joelmathewsssss/HammerHacks-II-Badge-PCB/assets/bird.png

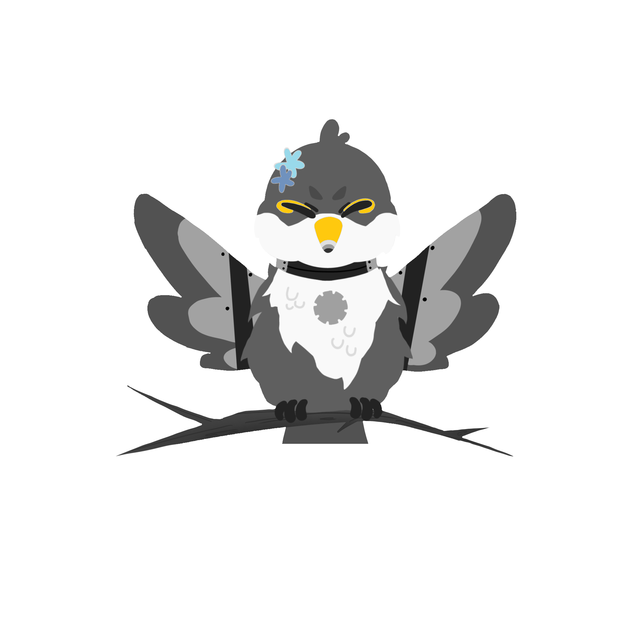
assets/bird.png
