joelmathewsssss/HammerHacks-II-Badge-PCB/assets/PICS/image.png

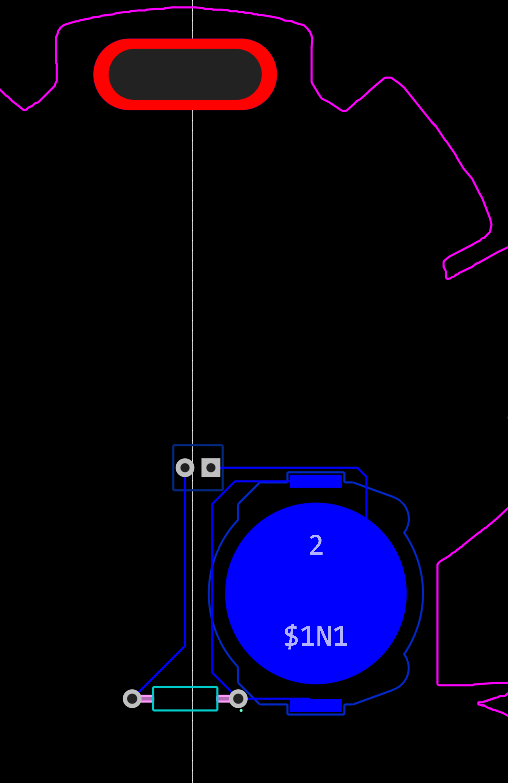
assets/PICS/image.png
