joelmathewsssss/HammerHacks-II-Badge-PCB/assets/PICS/PXL_20260712_225930694.jpg

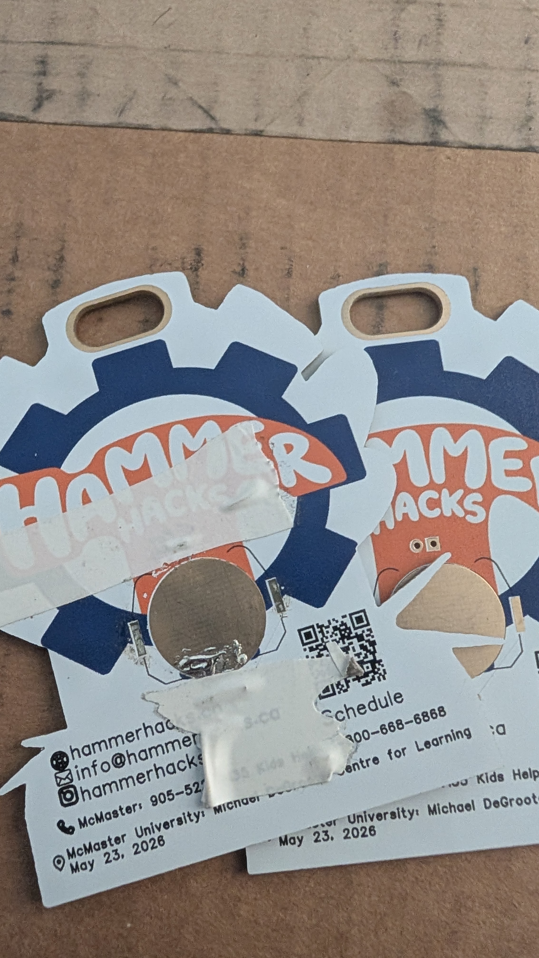
assets/PICS/PXL_20260712_225930694.jpg
