joelmathewsssss/HammerHacks-II-Badge-PCB/assets/PICS/PXL_20260712_232706811.jpg

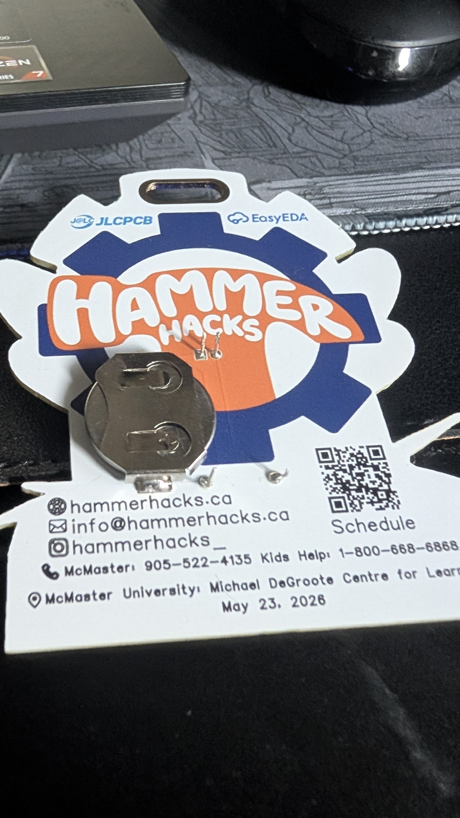
assets/PICS/PXL_20260712_232706811.jpg
