joelmathewsssss/HammerHacks-II-Badge-PCB/assets/PICS/Screenshot 2026-03-13 092637.png

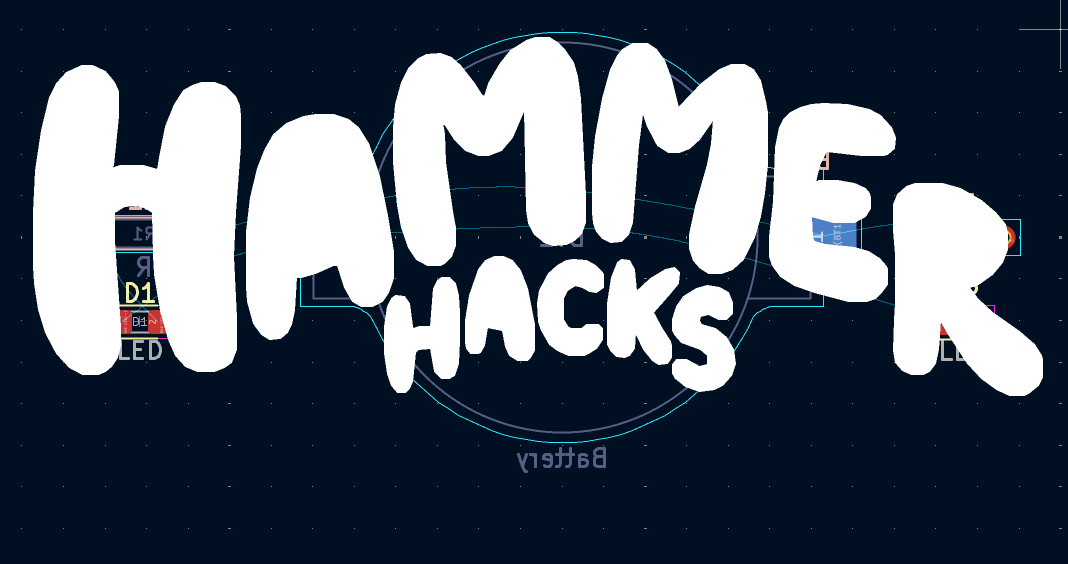
assets/PICS/Screenshot 2026-03-13 092637.png
