joelmathewsssss/HammerHacks-II-Badge-PCB/assets/PICS/Screenshot 2026-03-14 190404.png

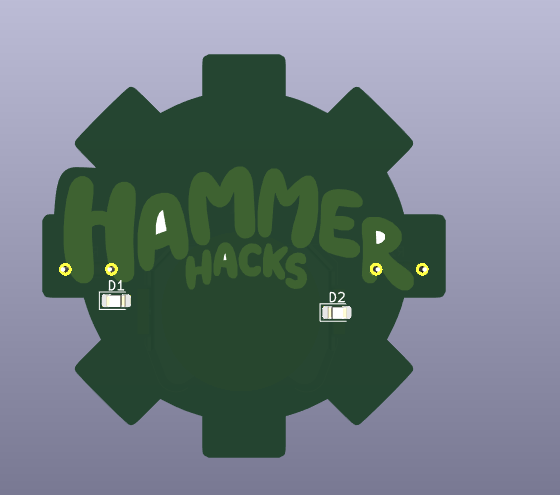
assets/PICS/Screenshot 2026-03-14 190404.png
