joelmathewsssss/HammerHacks-II-Badge-PCB/assets/PICS/Screenshot 2026-03-18 231449.png

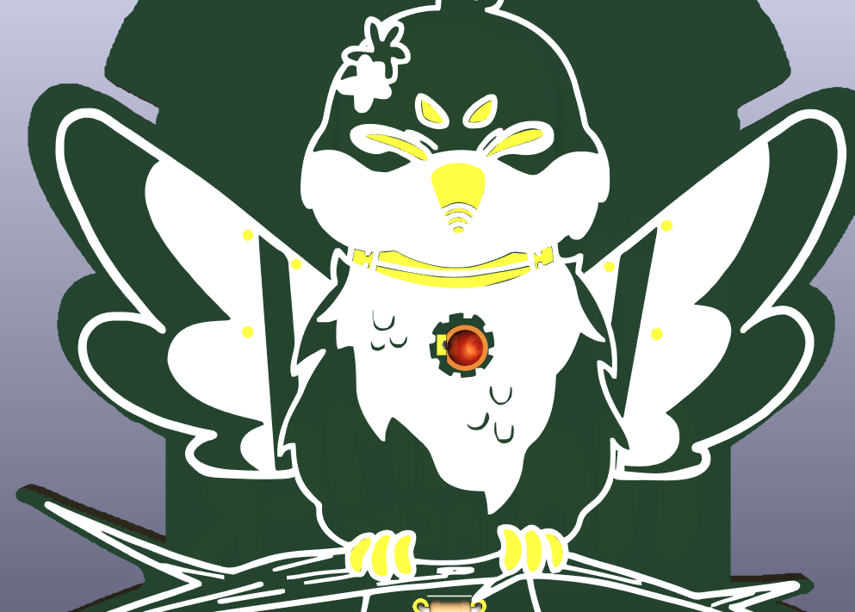
assets/PICS/Screenshot 2026-03-18 231449.png
