joelmathewsssss/HammerHacks-II-Badge-PCB/assets/PICS/Screenshot 2026-03-18 235800.png

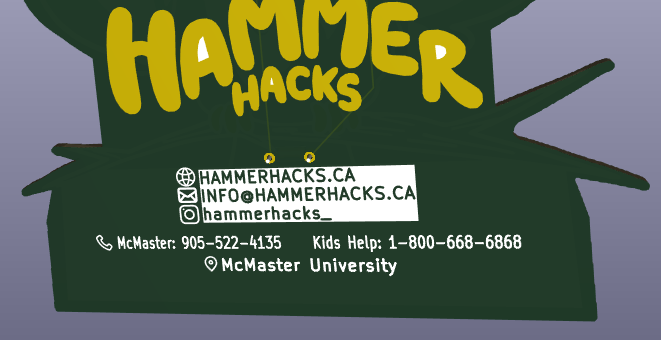
assets/PICS/Screenshot 2026-03-18 235800.png
