joelmathewsssss/HammerHacks-II-Badge-PCB/assets/PICS/Screenshot 2026-03-19 003215.png

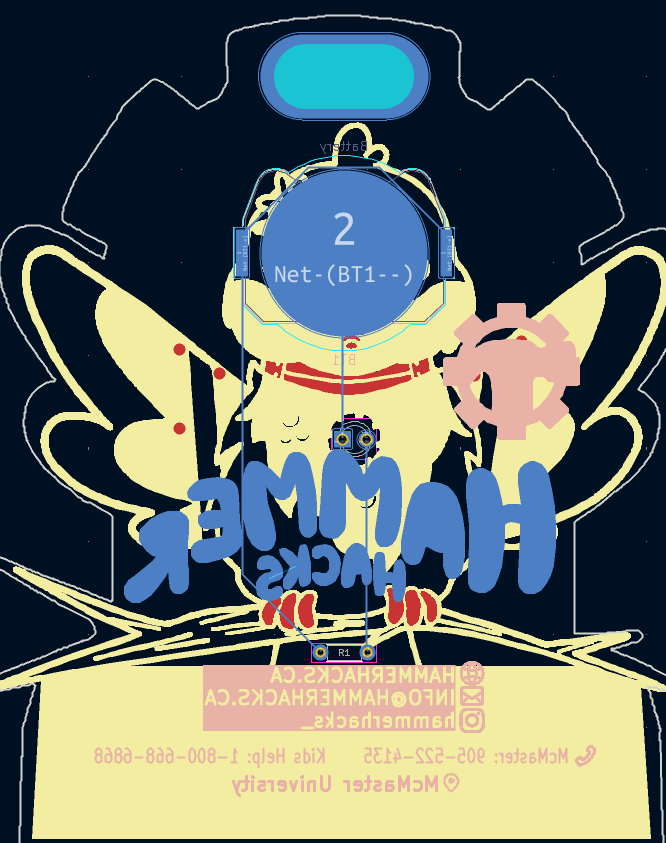
assets/PICS/Screenshot 2026-03-19 003215.png
