joelmathewsssss/HammerHacks-II-Badge-PCB/assets/PICS/Screenshot 2026-03-19 223616.png

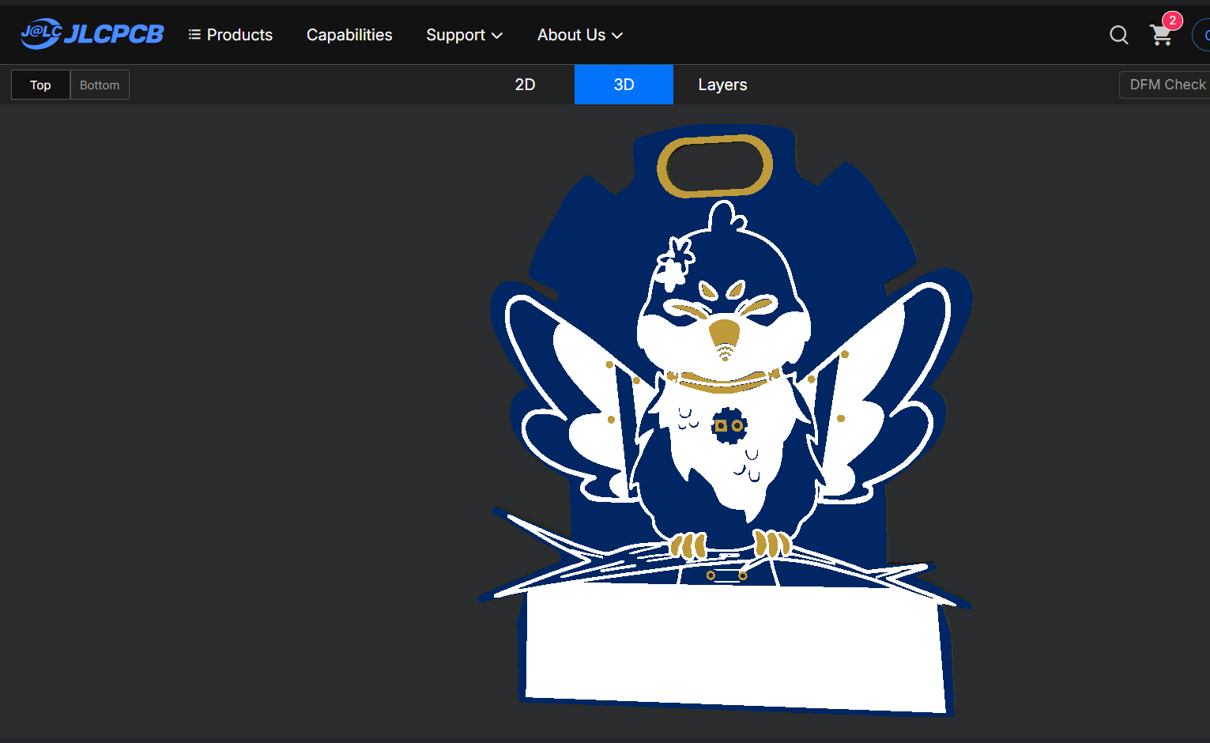
assets/PICS/Screenshot 2026-03-19 223616.png
