joelmathewsssss/HammerHacks-II-Badge-PCB/assets/PICS/Screenshot 2026-03-26 190704.png

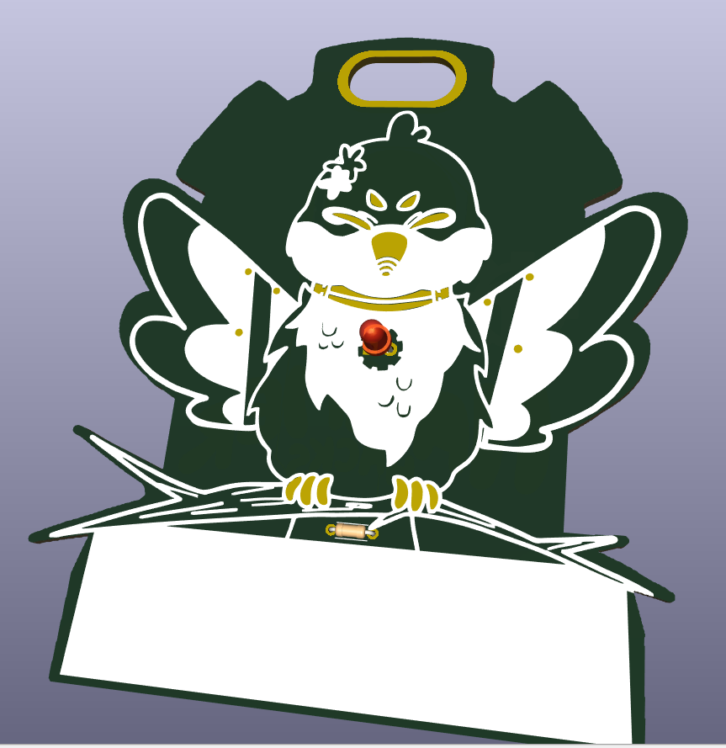
assets/PICS/Screenshot 2026-03-26 190704.png
