joelmathewsssss/HammerHacks-II-Badge-PCB/assets/PICS/Screenshot 2026-04-06 212040.png

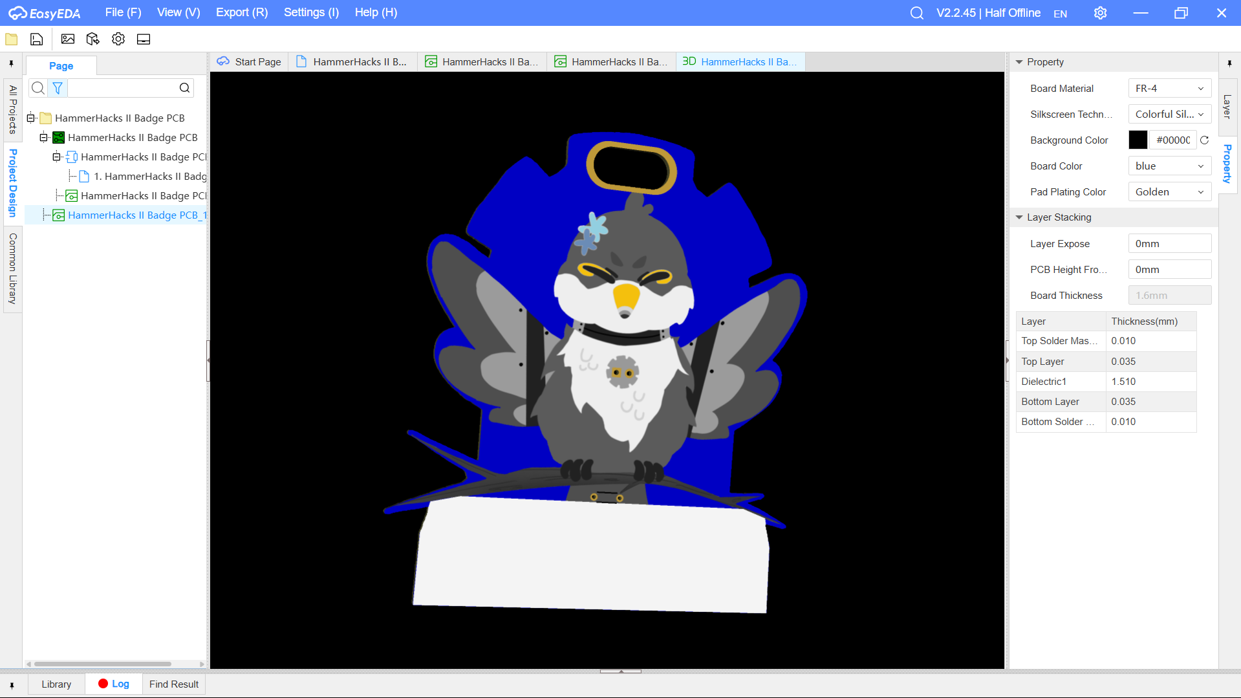
assets/PICS/Screenshot 2026-04-06 212040.png
