joelmathewsssss/HammerHacks-II-Badge-PCB/assets/PICS/Screenshot 2026-04-06 233326.png

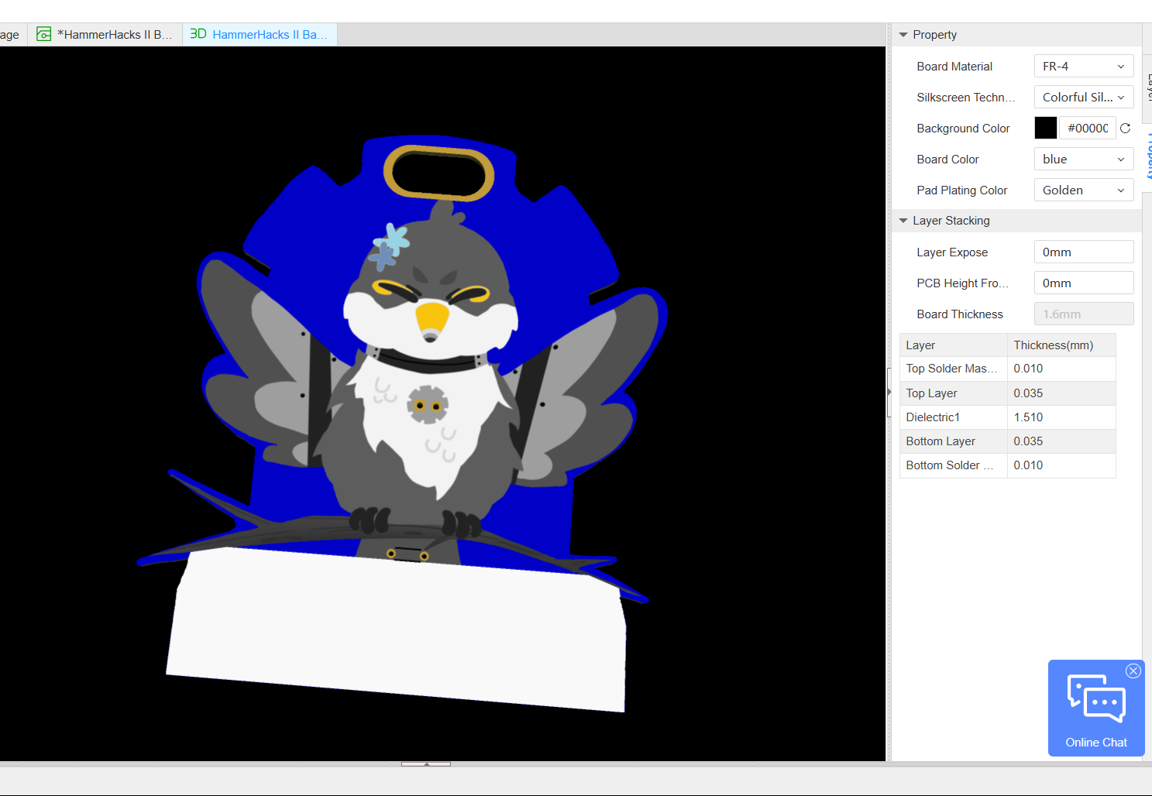
assets/PICS/Screenshot 2026-04-06 233326.png
