joelmathewsssss/HammerHacks-II-Badge-PCB/assets/PICS/Screenshot 2026-04-07 103023.png

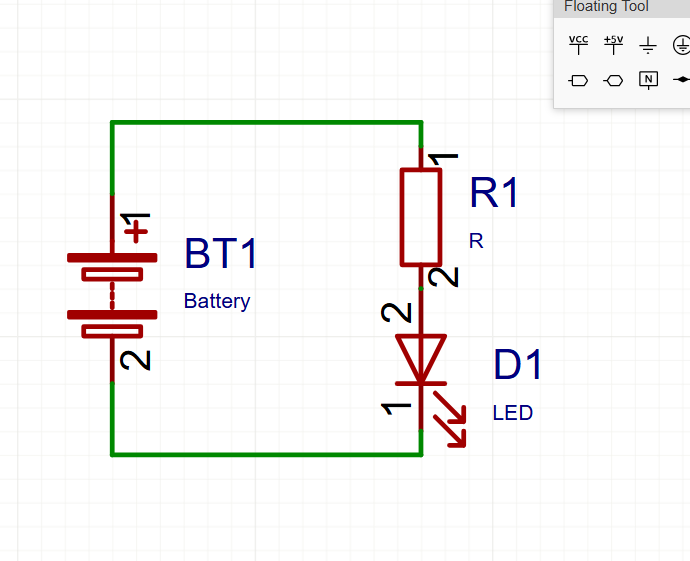
assets/PICS/Screenshot 2026-04-07 103023.png
