joelmathewsssss/HammerHacks-II-Badge-PCB/assets/PICS/Screenshot 2026-04-07 103103.png

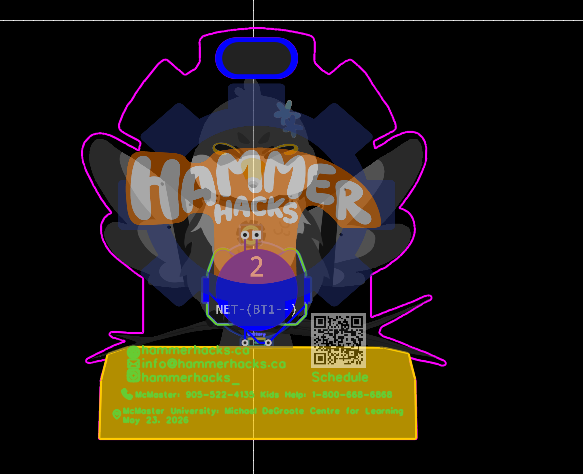
assets/PICS/Screenshot 2026-04-07 103103.png
