joelmathewsssss/HammerHacks-II-Badge-PCB/assets/PICS/Screenshot 2026-05-07 062815.png

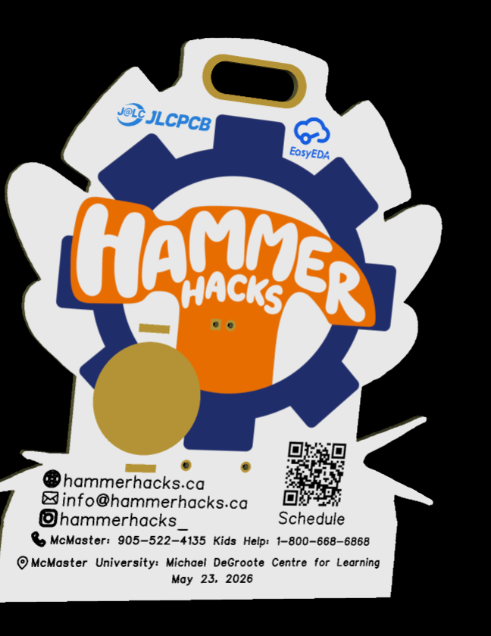
assets/PICS/Screenshot 2026-05-07 062815.png
