joelmathewsssss/HammerHacks-II-Badge-PCB/assets/PICS/Screenshot 2026-07-12 192727.png

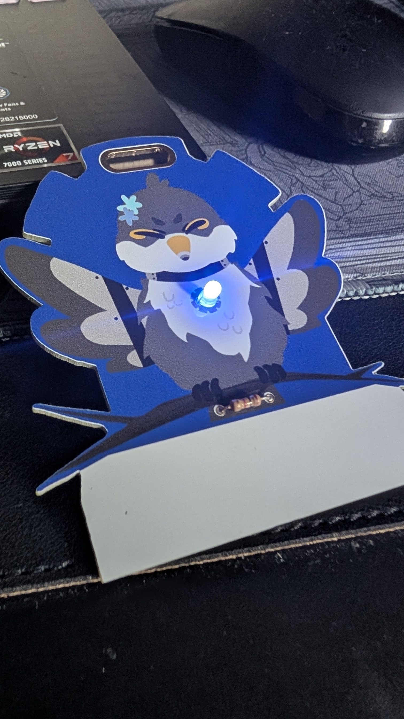
assets/PICS/Screenshot 2026-07-12 192727.png
