joelmathewsssss/HammerHacks-II-Badge-PCB/assets/silkscreen.png

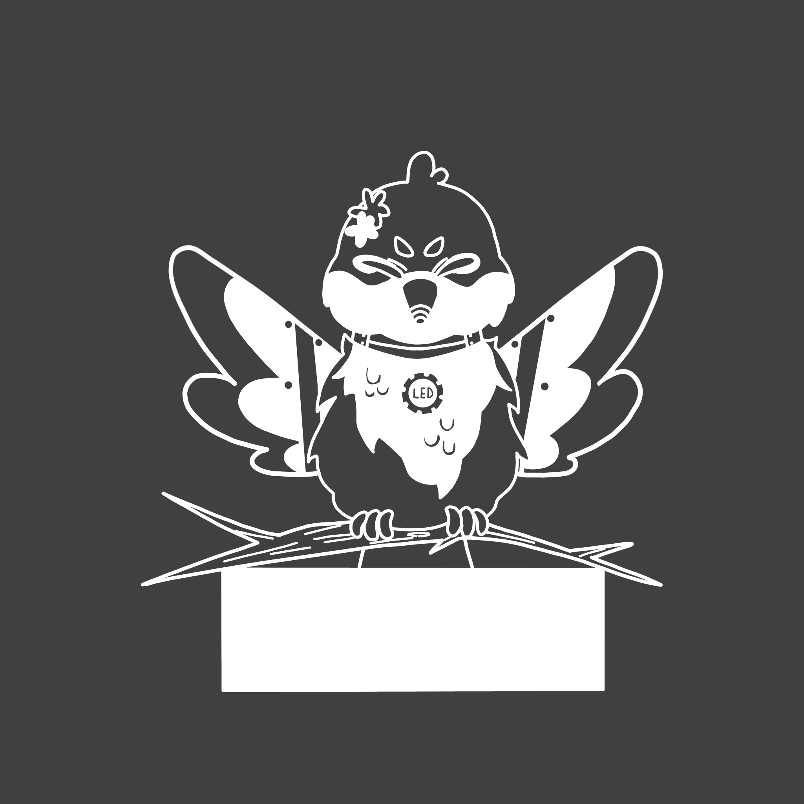
assets/silkscreen.png
